Forestierr/TPI-Controle-lumieres-knx/1_Documentation/3_PDF/camera/camera_Detection_Entry_entry_detect.py.pdf

1 | """entry_detect.py | Robin Forestier | 09.03.2022
3 | This file is used to detect entry and exit. It uses DoorSelect & PersonneDetect &
PersonneTracking.
4 | """
5
6 | import | | math
7 | import | | pickle
8 | import | | time
9 | from | | datetime | | import | | datetime
10 | from | | os | | import | | path
11
12 | import | | cv2
13 | import | | numpy | | as | | np
14 | import | | requests
15
16 | # import personally module
17 | from | | sample.door_select | | | | import | | DoorSelect
18 | from | | sample.personne_detect | | | | import | | PersonneDetect
19 | from | | sample.personne_tracking | | | | import | | PersonneTracking
20
21
22 | class | | DetectEntry:
23 | | """DetectEntry class is used to detect entry and exit."""
24 | | def | | __init__(self, | | | | | frame, | doors, | | fleches):
25 | | """The function takes in the frame, the doors and the arrows to calcul of a
| personne is going in or out.
26
27 | :param frame: The image frame that the camera captured
28 | :type frame: numpy.ndarray
29 | :param doors: a list of tuples, each tuple is a door, with the first element
| being the x-coordinate of the
30 | center of the door, and the second element being the y-coordinate of the
| center of the door
31 | :type doors: list
32 | :param fleches: a list of tuples, each tuple is a pair of points, the first
| point is the center of the arrow,
33 | the second is the tip of the arrow
34 | :type fleches: list
35 | """
36
37 | | self.img | | | | = | | frame
38 | | self.doors | | | | = | | doors
39 | | self.fleches | | | | = | | fleches
40
41 | | self.angle | | | | = | | []
42 | | self.angle2 | | | | = | | []
43
44 | | def | | verify_door_pos(self):
45 | | | | # TODO add door_detect
46 | | pass
47
48 | | def | | calculate(self, | | | | | d_select):
49 | | """Calculate the angle between the center of the door and the arrow
50
51 | :param d_select: the door_select object
52 | :type d_select: DoorSelect
53 | """
54
55 | | n_door | | = | | 0
56
57 | | # Used to set the image and the doors and arrows position to the DoorSelect
| object.
58 | | d_select.img | | | | = | | frame
59 | | d_select.doors | | | | = | | pos
60 | | d_select.fleches | | | | = | | f_pos
61
62 | | for | | door | | in | | zip(*[iter(self.doors)] | | | | | | * | 4):
63 | | rect | | = | | np.zeros((4, | | | | | 2), | | dtype="float32")
65 | # Summing the door points.
66 | s | = | np.sum(door, | axis=1)

67 | # It's calculating the minimum and maximum value of the door.
68 | rect[0] | = | door[np.argmin(s)]
69 | rect[2] | = | door[np.argmax(s)]
71 | | # It's calculating the difference between the door points.
72 | | diff | = | | np.diff(door, | | | | | | | axis=1)
73 | | # It's calculating the minimum and maximum value of the door.
74 | | rect[1] | | | | = | | door[np.argmin(diff)]
75 | | rect[3] | | | | = | | door[np.argmax(diff)]
76
77 | | # It's converting the rect from float to int.
78 | | rect | = | | rect.astype(int)
79
80 | | # It's calculating the center of th bottom of the door.
81 | | center | = | | (int((rect[3][0] | | | | | | | | | + | | rect[2][0]) | | | | / | 2), | int((rect[3][1] | +
| rect[2][1]) | | | | | | / | | 2))
82
83 | | # It's calculating the angle between the center of the door and the
| bottom of the door.
84 | | y | = | | center[1] | | | | | - | | rect[2][1]
85 | | x | = | | center[0] | | | | | - | | rect[2][0]
86 | | angle | = | | math.atan2(y, | | | | | | | x) | | * | | 180 | | / | math.pi
87
88 | | # It's making sure that the angle is between 0 and 360.
89 | | if | angle | | < | | 0:
90 | | angle | = | | 360 | | + | | angle
91
92 | | self.angle.append(angle)
93
94 | | # It's calculating the angle between the center of the door and the tip
| of the arrow.
95 | | y | = | | center[1] | | | | | - | | self.fleches[n_door][1]
96 | | x | = | | center[0] | | | | | - | | self.fleches[n_door][0]
97 | | angle2 | = | | math.atan2(y, | | | | | | | x) | | * | | 180 | | / | math.pi
98
99 | | # It's making sure that the angle is between 0 and 360.
100 | | if | angle2 | | < | | 0:
101 | | angle2 | = | | 360 | | + | | angle2
102
103 | | self.angle2.append(angle2)
104
105 | | n_door | = | | n_door | | + | | 1
106
107 | | def | calc_in_out(self, | | | | | frame, | | | d_select, | | tracking, | | | info):
108 | | """Calculate if the person is going inside or outside
109
110 | :param frame: the frame from your video file or directly from your webcam
111 | :type frame: numpy.ndarray
112 | :param d_select: the door selection object
113 | :type d_select: DoorSelect
114 | :param tracking: the PersonneTracking object
115 | :type tracking: PersonneTracking
116 | :param info: an object of the Info class, which is used to store information
| about the people detected in the frame
117 | :type info: Info
118 | """
119
120 | | # It's drawing the doors on the frame.
121 | | d_select.img | | | = | | frame
122 | | d_select.draw_door()
123
124 | | n_door | = | | 0
125
126 | | for | door | | in | | zip(*[iter(d_select.doors)] | | | | | | | | * | | 4):
127 | | door | = | | np.array(door)
128 | | x, | | y, | | | w, | | | h | | = | cv2.boundingRect(door)
129
130 | | n | = | | 0
132 | for | a | in | tracking.angle:
133 | # It's checking if the person is in the door.
134 | if | x | < | tracking.centroide[n][0] | < | x | + | w | and | y | <

| tracking.centroide[n][1] | | | | | | < | | y | | + | | h:
135 | | if | | self.angle[n_door] | | | | - | | 180 | | < | | 0:
136 | | angle2 | | = | 360 | - | (self.angle[n_door] | | | | | | | | + | | 180)
137 | | else:
138 | | angle2 | | = | self.angle[n_door] | | | | | - | | 180
139
140 | | if | | 10 | < | a | - | | angle2 | | < | | 170:
141 | | if | | self.angle2[n_door] | | | | - | | angle2 | | < | | 170:
142 | | info.queue.append([time.time(), | | | | | | | | 0, | | | n_door, | | | n])
143 | | else:
144 | | info.queue.append([time.time(), | | | | | | | | 1, | | | n_door, | | | n])
145 | | elif | | 190 | < | a | - | | angle2 | | < | | 350:
146 | | if | | self.angle2[n_door] | | | | - | | angle2 | | < | | 170:
147 | | info.queue.append([time.time(), | | | | | | | | 1, | | | n_door, | | | n])
148 | | else:
149 | | info.queue.append([time.time(), | | | | | | | | 0, | | | n_door, | | | n])
150 | | else:
151 | | pass
152
153 | | n | | = | n | + | 1
154 | | n_door | | = | n_door | + | 1
155
156
157 | class | | info:
158 | | """class info is used for sorting the value from calc_in_out (class
| DetectEntry)"""
159 | | def | | __init__(self):
160 | | """is a list of the last in/out value.
161 | [time, in (1) / out (0), door_num, personne_num]
162 | """
163 | | self.queue | | | = | []
164
165 | | def | | verify(self):
166 | | """Verify check all value in queue list.
167 | First I delete all value is too old (more than 5sec).
168 | After if we have 3 or more same detection, a validation is sent (return 0 or
| 1)
169
170 | :return: 0 or 1
171 | :rtype: int
172 | """
173
174 | | # It's checking if there is more than 3 detection.
175 | # | If there is, it's checking which door has the most detection.
176 | # | If there is more than one door with the same number of detection, it's
| checking which person is the
177 | | # closest to the center of the door.
178 | # | If there is only one door with the most detection, it's checking if the
person is going inside or outside.
179 | # | If the person is going inside, it's sending 1 to the server.
180 | # | If the person is going outside, it's sending 0 to the server.
181 | if | len(self.queue) | | | >= | 3:
182 | # It's converting the queue list to a numpy array.
183 | out | = | np.array(self.queue).T
184 | temp_ex | = | []
185
186 | # It's converting the array to int.
187 | out | = | out.astype(int)
188
189 | for | t | in | out[0]:
190 | if | t | < | out[0][len(self.queue) | | | | | | - | 1] | - | 5:
191 | temp_ex.append(np.where(out[0] | | | | | | == | | t))
192
193 | # It's deleting the value in the array that are in temp_ex.
194 | out | = | np.delete(out, | | | temp_ex, | | axis=1)
195
196 | inout | = | np.bincount(out[1]).argmax()
198 | if | max(np.bincount(out[1])) | | | | <= | max(np.bincount(out[2])) | and | \
199 | max(np.bincount(out[1])) | | | | <= | max(np.bincount(out[3])):
200 | self.queue | | = | []

202 | # It's returning the value of the verification of the queue list.
203 | return | inout
206 | def | | send(info):
207 | | """Send the data to the server
208
209 | :param info: the information to send
210 | :type info: int
211 | """
212
213 | | # It's getting the current time.
214 | | t | | = | | datetime.now()
215 | | current_time | | = | | t.strftime("%H:%M")
216
217 | | # It's opening the file /sys/class/thermal/thermal_zone0/temp and reading the
| temperature.
218 | | try:
219 | | with | | open('/sys/class/thermal/thermal_zone0/temp', | | | | | 'r') | | | as | | ftemp:
220 | | temp | | = | | int(int(ftemp.read()) | | | | | | | | | / | | 1000)
221 | | except | | OSError:
222 | | temp | | = | | 0
223
224 | | # It's creating a string that will be sent to the server.
225 | | data | | = | | "{}{:03d}{}".format(current_time, | | | | | | | temp, | | | info)
226 | | data | | = | | {'data': | | | | '$,RPWCSD,{:03d},{},0*'.format(len(data), | | | | | | | | | data)}
227
228 | | try:
229 | | # It's sending the data to the server.
230 | | r | | = | | requests.post("http://172.16.32.133/camera", | | | | | | | data=data, | | | | | timeout=0.5)
231
232 | | # This is checking if the status code is bigger than 299. If it is, it's
| printing an error message.
233 | | if | | r.status_code | | | | > | | 299:
234 | | print("[Error] Communication error")
235 | | else:
236 | | # It's getting the data from the server.
237 | | data | | = | | r.text
238 | | # if the data is a correct trame ($,...,*)
239 | | if | | data[0] | | | | | == | | "$" | | and | | data[::-1][0] | | | | | | == | "*":
240 | | data | | = | | data.split(',')
241
242 | | # Communication OK
243 | | if | | data[1] | | | | | == | | "RPWCOK":
244 | | print("ok")
245 | | # Communication Error
246 | | if | | data[1] | | | | | == | | "RPWCER":
247 | | print("[ERROR] The cam had send a bad trame.")
248
249 | | # It's catching the error if the server is not available.
250 | | except | | requests.exceptions.RequestException | | | | | | as | | e:
251 | | print(e)
252
253
254 | if | | __name__ | | == | | '__main__':
255 | | # It's opening the webcam.
256 | | cap | | = | | cv2.VideoCapture(0)
257
258 | | # It's getting the frame from the webcam.
259 | | _, | | | frame | | = | | cap.read()
260
261 | | # It's resizing the frame to 640x480.
262 | | frame | | = | | cv2.resize(frame, | | | | | | | (640, | | | | 480), | | | interpolation=cv2.INTER_AREA)
263
264 | | # This is checking if the file "doors.pickle" exists. If it doesn't, it's
| creating a new DoorSelect object and
265 | # | saving the doors and the arrows position in the file "doors.pickle".
266 | # | If the file "doors.pickle" exists, it's loading the data from the file.
267 | if | not | path.exists("doors.pickle"):
268 | d_select | = | DoorSelect(frame)
269 | pos | = | d_select.doors
270 | f_pos | = | d_select.fleches

271 | else:
272 | d_select | = | | DoorSelect()
273 | with | open('doors.pickle', | | | | 'rb') | as | f:
274 | pos, | | f_pos | | = | pickle.load(f)
276 | | # It's creating a PersonneDetect object and storing it in the variable `detect`.
277 | | detect | = | | PersonneDetect()
278 | | # It's creating a PersonneTracking object and storing it in the variable
| `tracking`.
279 | | tracking | = | | PersonneTracking()
280 | | # It's creating an object of the class DetectEntry and storing it in the
| variable `entry`.
281 | | entry | = | | DetectEntry(frame, | | | | pos, | | | f_pos)
282 | | # It's calculating the angle between the center of the door and the arrow.
283 | | entry.calculate(d_select)
284 | | # It's creating an object of the class `info` and storing it in the variable
| `inf`.
285 | | inf | = | | info()
286
287 | | while | True:
288 | | # This is checking if the video is over. If it is, it's reseting the frame
| to the first frame.
289 | | if | cap.get(cv2.CAP_PROP_POS_FRAMES) | | | | | | | | == | | cap.get(cv2.CAP_PROP_FRAME_COUNT):
290 | | cap.set(cv2.CAP_PROP_POS_FRAMES, | | | | | | | 0)
291
292 | | # It's getting the frame from the webcam.
293 | | _, | | frame | | = | | cap.read()
294
295 | | # It's resizing the frame to 640x480.
296 | | frame | = | | cv2.resize(frame, | | | | | | (640, | | | 480), | interpolation=cv2.INTER_AREA)
297
298 | | # It's detecting people in the frame.
299 | | frame | = | | detect.personne_detect(frame)
300 | | # It's calculating the centroid of the detected people.
301 | | tracking.calc_centroide(frame, | | | | | | detect.detected)
302 | | # It's calculating if the person is going inside or outside.
303 | | entry.calc_in_out(frame, | | | | | | d_select, | | tracking, | | | inf)
304
305 | | # It's checking if the person is going inside or outside.
306 | | # If the person is going inside, it's sending 1 to the server.
307 | | # If the person is going outside, it's sending 0 to the server.
308 | | inout | = | | inf.verify()
309
310 | | if | inout | | == | | 1:
311 | | print("[INFO] Entrée")
312 | | send(inout)
313 | | elif | inout | | == | | 0:
314 | | print("[INFO] Sortie")
315 | | send(inout)
316
317 | | # It's showing the image in a window.
318 | | cv2.imshow("image", | | | | | | frame)
319
320 | | # It's checking if the user press the key "q". If it is, it's breaking the
| loop.
321 | | if | cv2.waitKey(100) | | | | | | == | | ord("q"):
322 | | break
323
324 | | # It's closing the webcam and the window.
325 | | cv2.destroyAllWindows()
326 | | cap.release()
327
