Forestierr/TPI-Controle-lumieres-knx/1_Documentation/1_XWiki/exemple_4.PNG

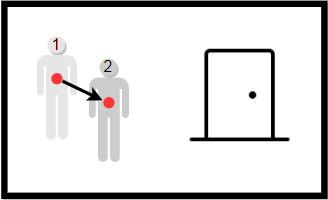
1_Documentation/1_XWiki/exemple_4.PNG
