Forestierr/TPI-Controle-lumieres-knx/1_Documentation/1_XWiki/page_1.png

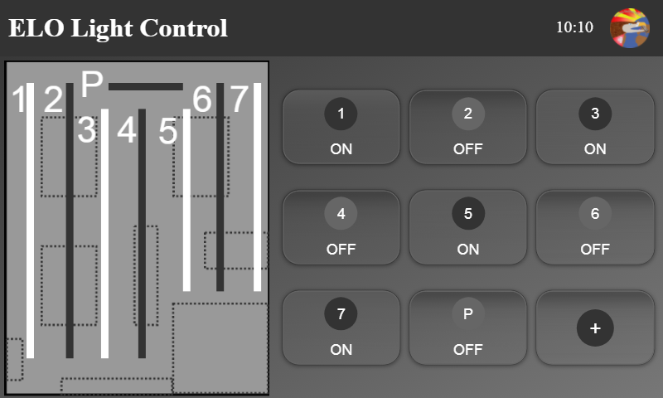
1_Documentation/1_XWiki/page_1.png
