Forestierr/TPI-Controle-lumieres-knx/1_Documentation/1_XWiki/page_2.png

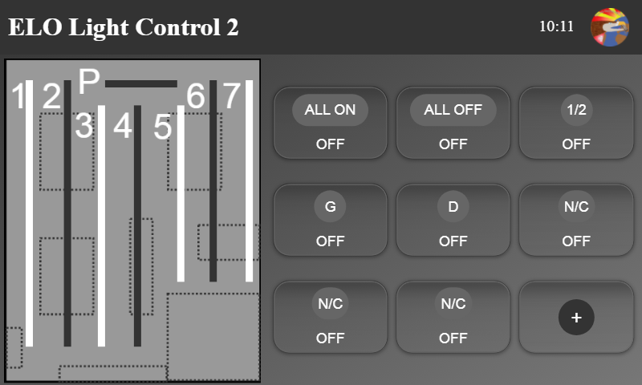
1_Documentation/1_XWiki/page_2.png
