Forestierr/TPI-Controle-lumieres-knx/1_Documentation/1_XWiki/table_1.png

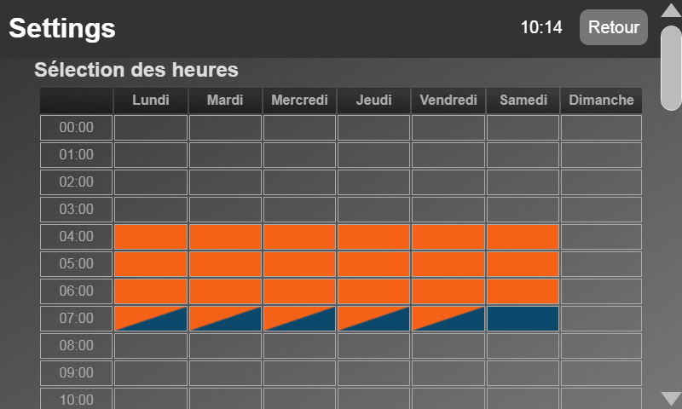
1_Documentation/1_XWiki/table_1.png
