Forestierr/TPI-Controle-lumieres-knx/1_Documentation/1_XWiki/cpu_usage_camera.PNG

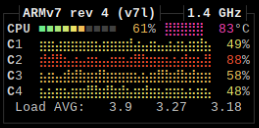
1_Documentation/1_XWiki/cpu_usage_camera.PNG
